Escape96X/MP_NETIO_BUTTON/kod/src/define.h

#ifndef _define_h_
#define _define_h_


// delky jsou vcetne 1 mezery pro ukonceni zapisu


#define SSID_POS 0
#define SSID_LEN 33
#define PASSWORD_POS 34
#define PASSWORD_LEN 100

#define IP_POSA 101
#define IP_POSB 289
#define IP_LEN 187
#define IP_JMP 17


#define HTTP_POSA 500
#define HTTP_LEN 1510
#define HTTP_POSB 2010
#define HTTP_JMP 151


#endif
